thazaubara/power-ESP/assets/221108_2301_OBJEKTIVGESEHEN_0954.jpg

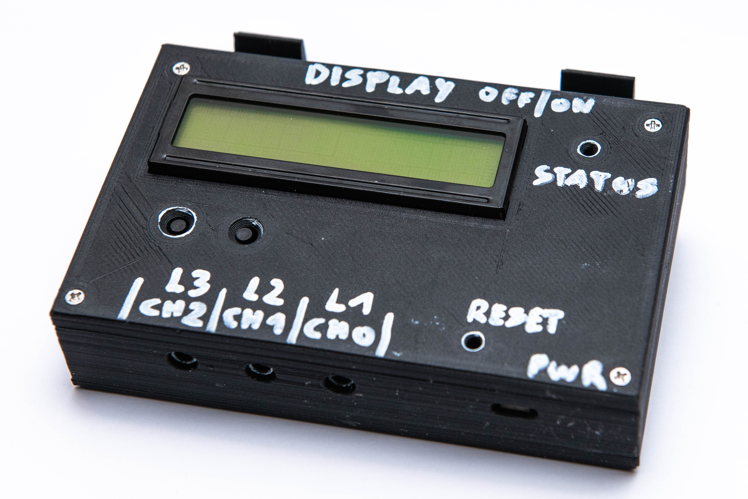
assets/221108_2301_OBJEKTIVGESEHEN_0954.jpg
