thazaubara/power-ESP/assets/221108_2302_OBJEKTIVGESEHEN_0958.jpg

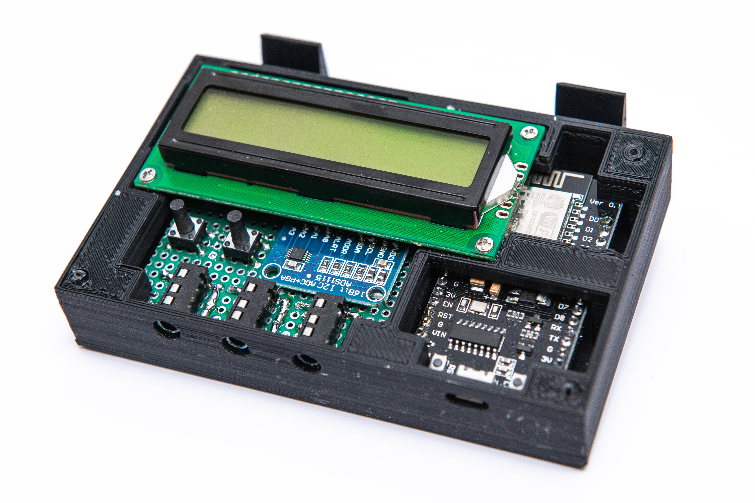
assets/221108_2302_OBJEKTIVGESEHEN_0958.jpg
