thazaubara/power-ESP/assets/221108_2313_OBJEKTIVGESEHEN_0966.jpg

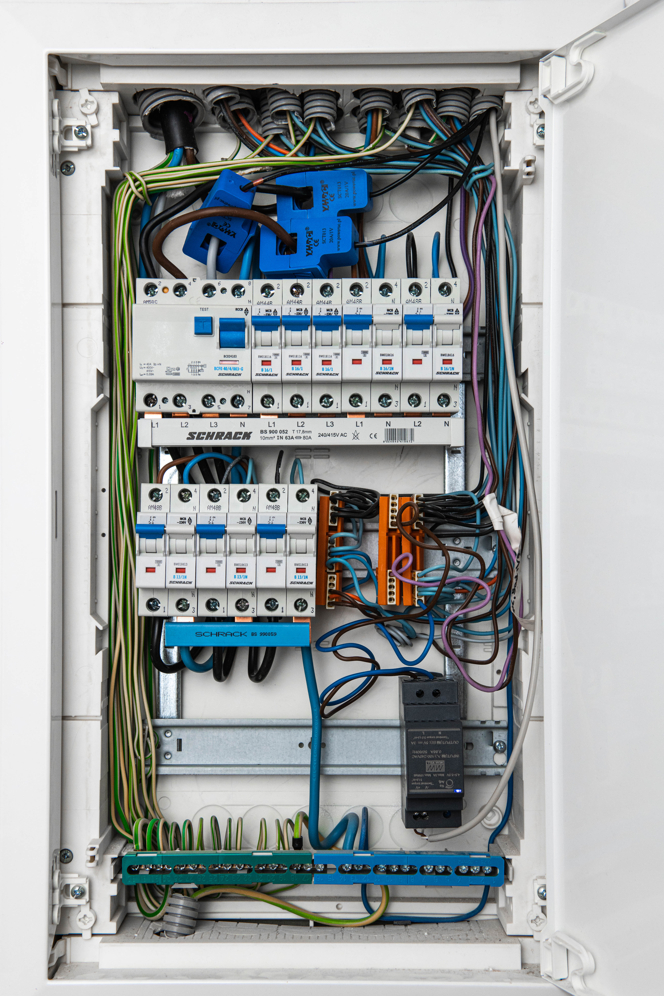
assets/221108_2313_OBJEKTIVGESEHEN_0966.jpg
