thazaubara/power-ESP/assets/IMG_9785.jpeg

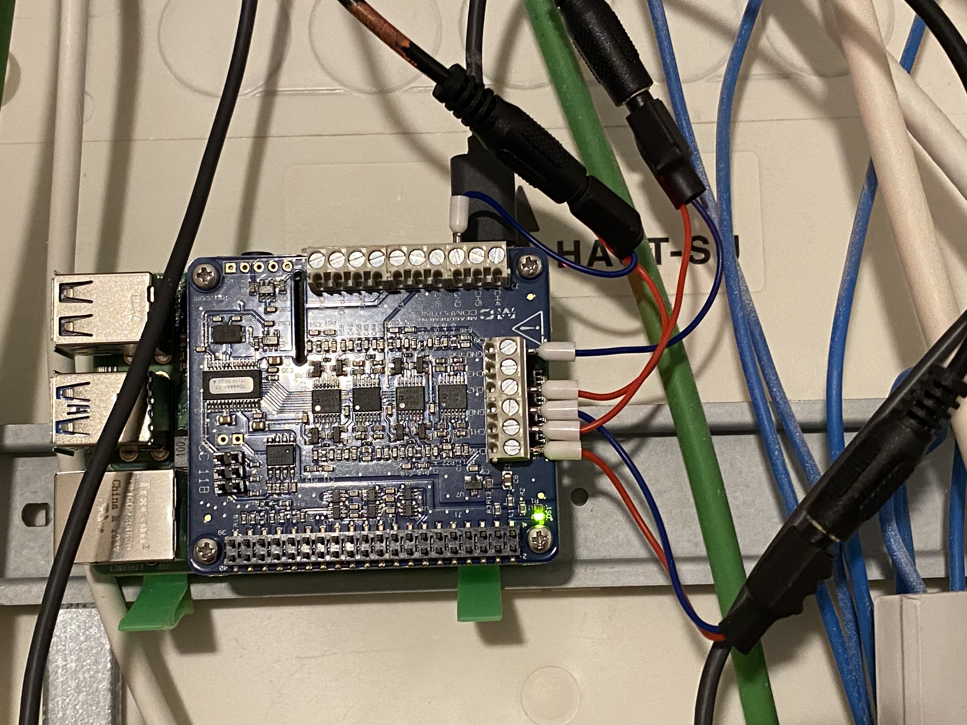
assets/IMG_9785.jpeg
