thazaubara/power-ESP/assets/IMG_9788.jpeg

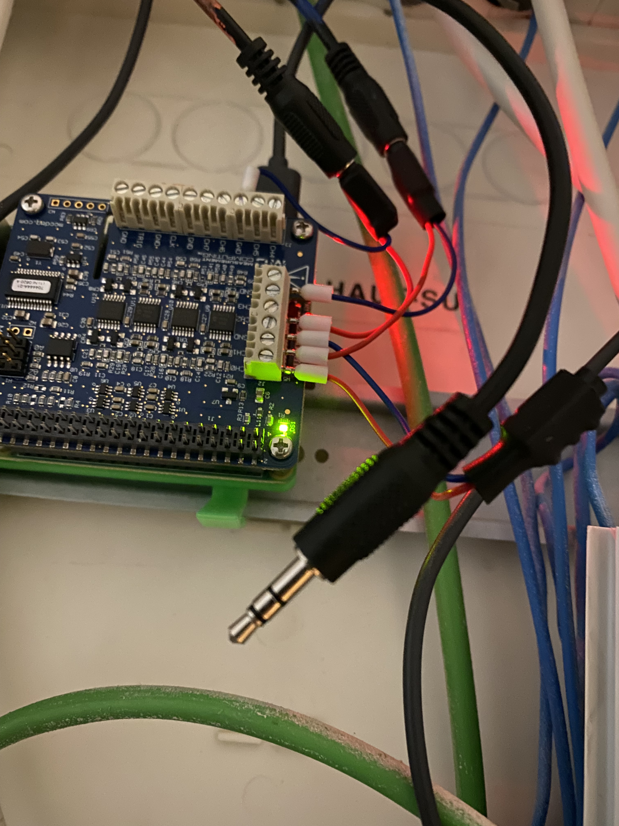
assets/IMG_9788.jpeg
