thazaubara/power-ESP/assets/IMG_9792.jpeg

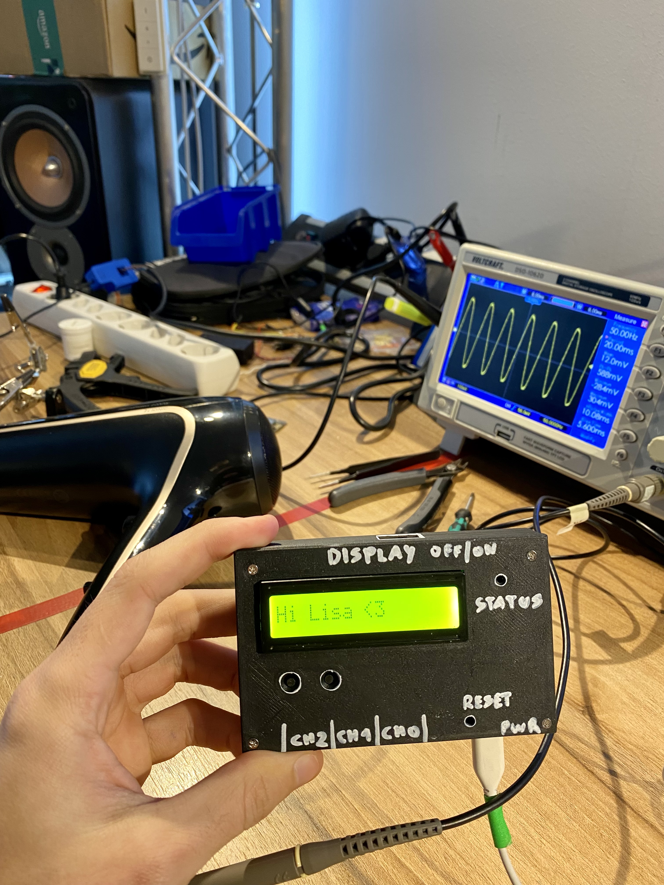
assets/IMG_9792.jpeg
