thazaubara/power-ESP/assets/IMG_9793.jpeg

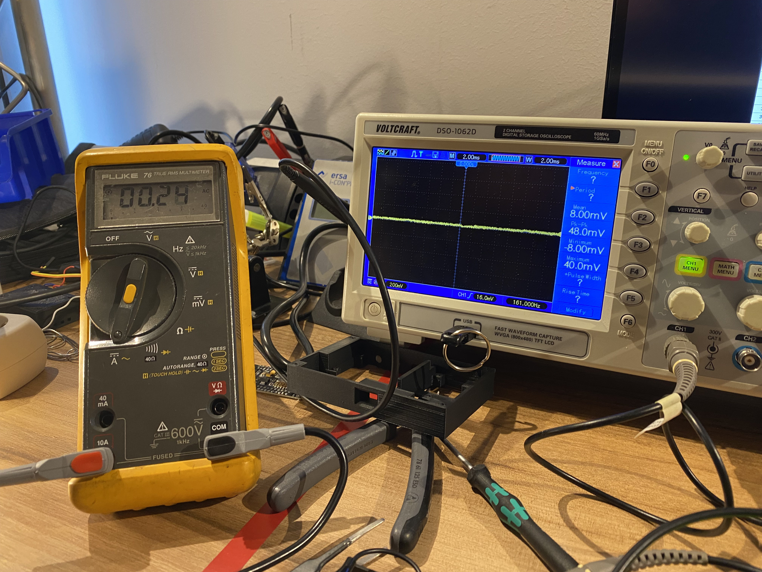
assets/IMG_9793.jpeg
