thazaubara/power-ESP/assets/IMG_9794.jpeg

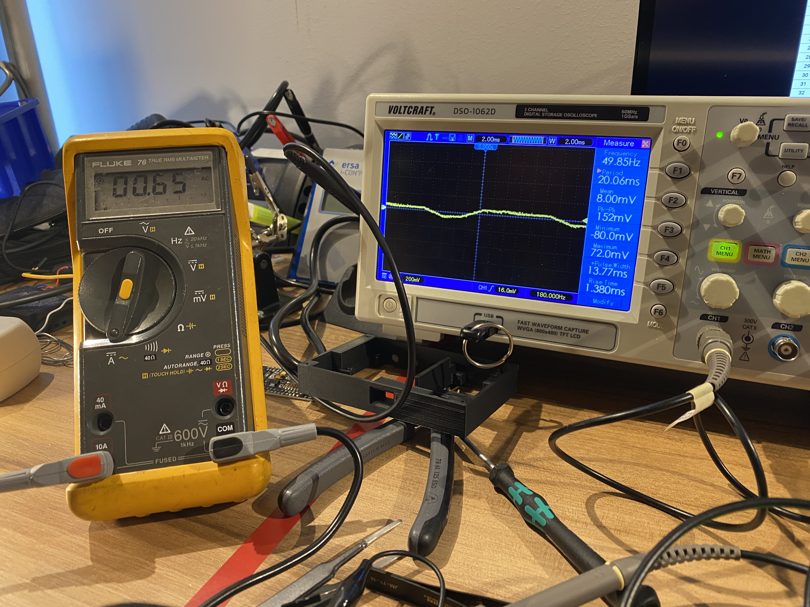
assets/IMG_9794.jpeg
