thazaubara/power-ESP/assets/IMG_9795.jpeg

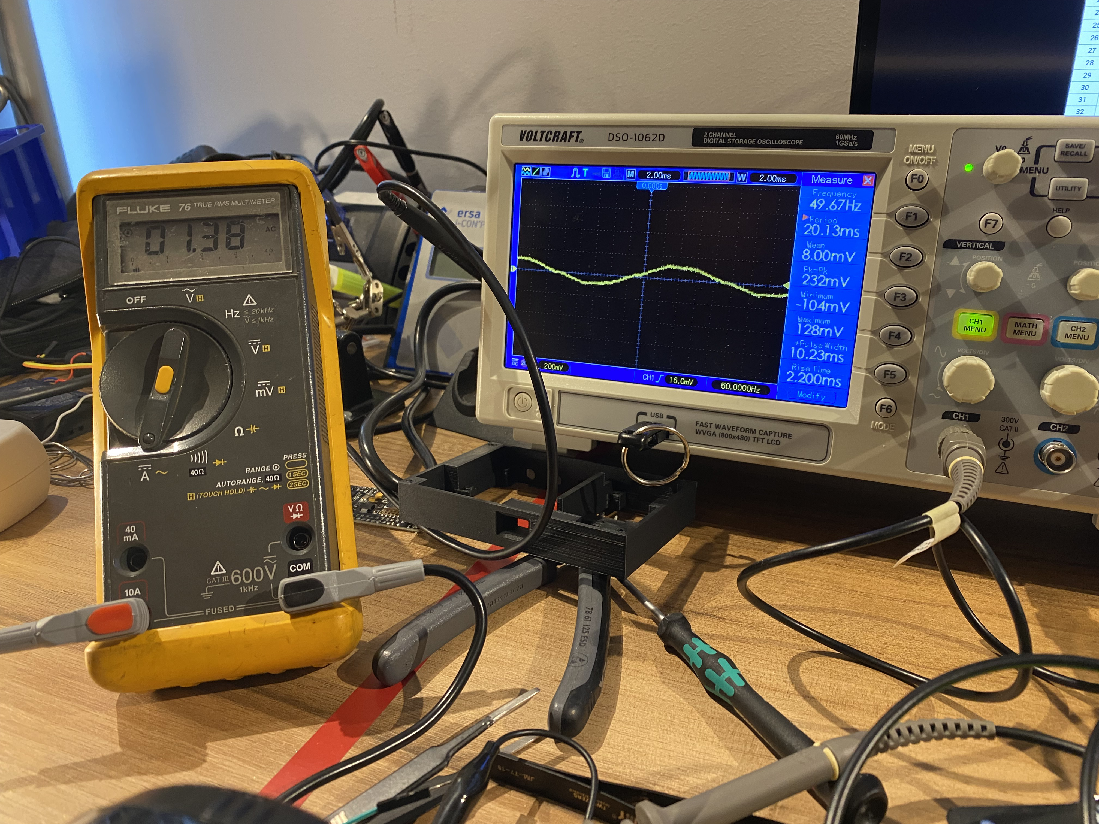
assets/IMG_9795.jpeg
