thazaubara/power-ESP/assets/IMG_9796.jpeg

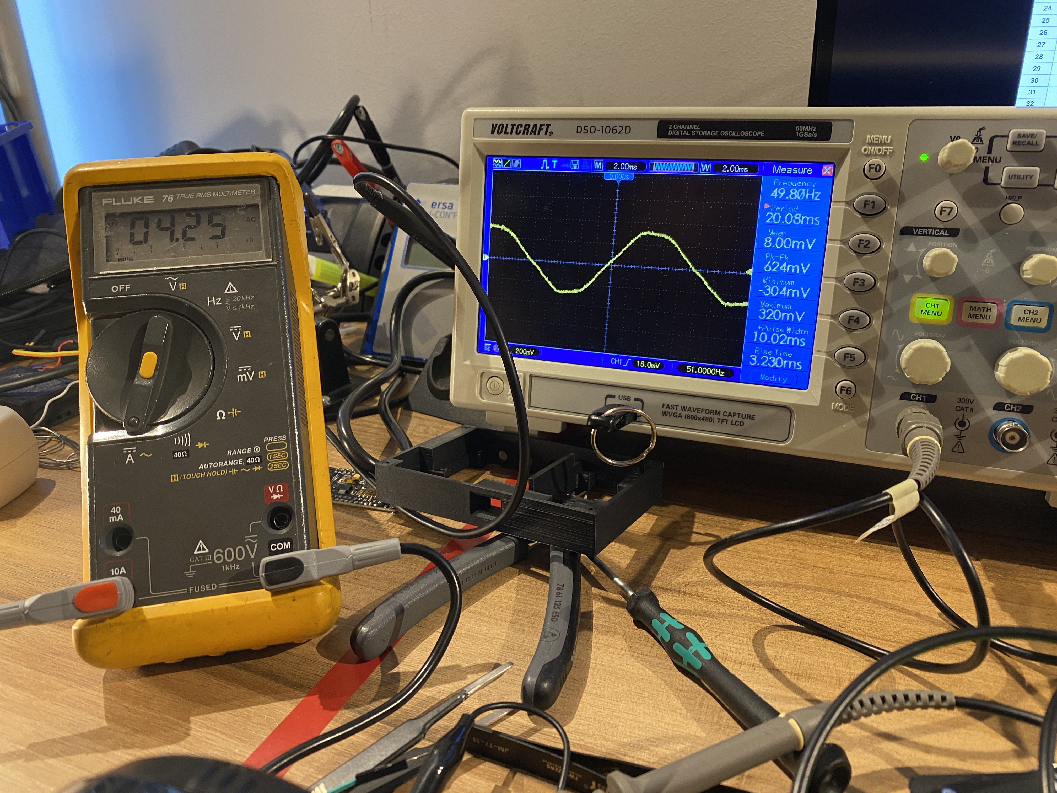
assets/IMG_9796.jpeg
