thazaubara/power-ESP/assets/IMG_9797.jpeg

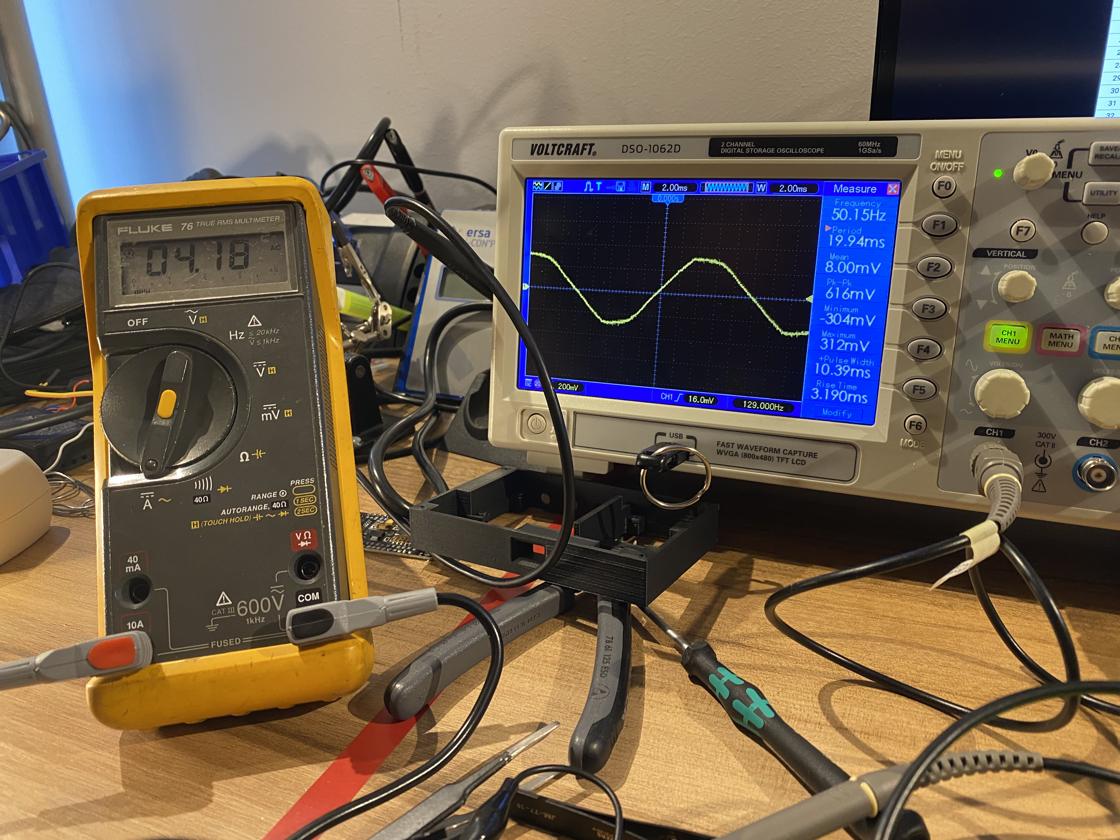
assets/IMG_9797.jpeg
