thazaubara/power-ESP/assets/IMG_9798.jpeg

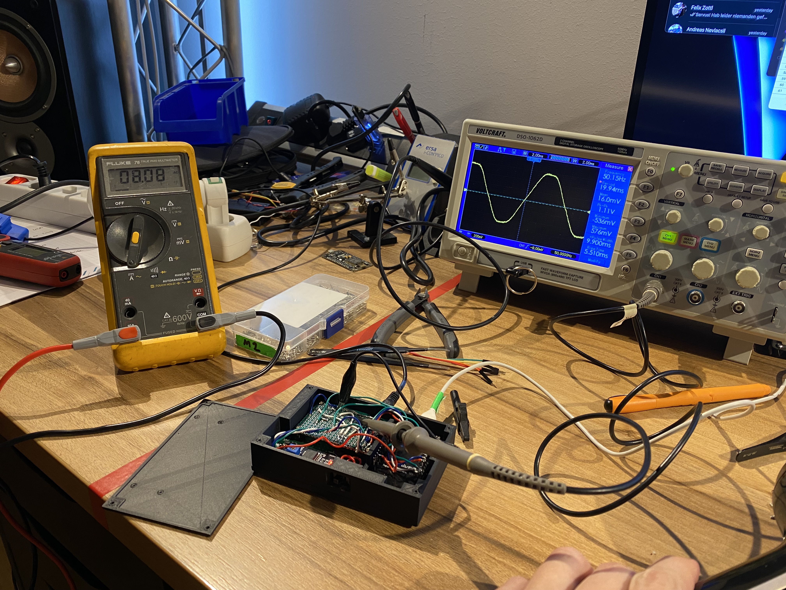
assets/IMG_9798.jpeg
