thazaubara/power-ESP/assets/voltcraft130_2.bmp

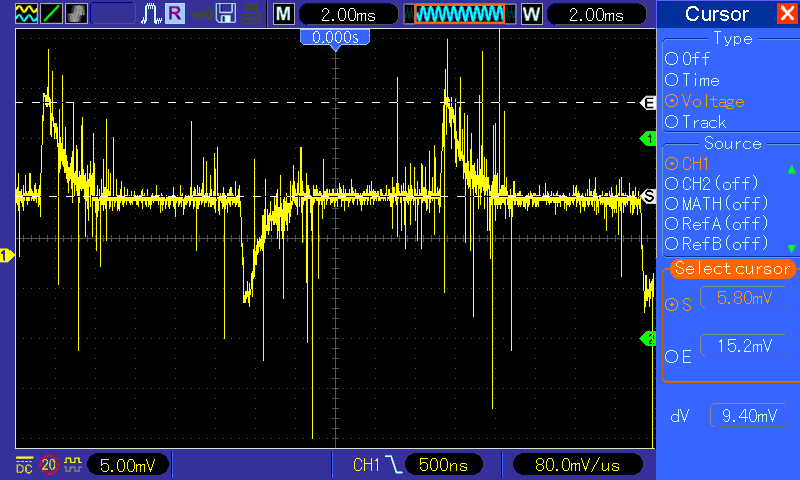
assets/voltcraft130_2.bmp
